blackjetrock/pak-gadget/eclipse/pak-gadget/scope_traces/rl_ram_siz1.jpg

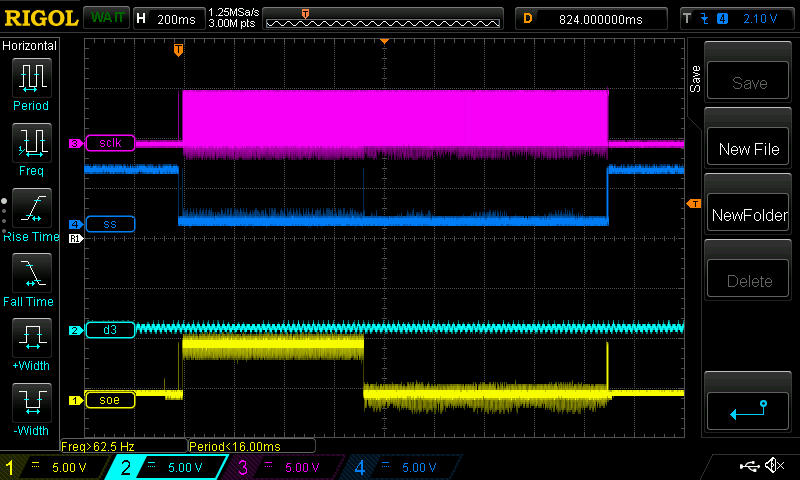
eclipse/pak-gadget/scope_traces/rl_ram_siz1.jpg
