blackjetrock/pak-gadget/eclipse/pak-gadget/scope_traces/g1.jpg

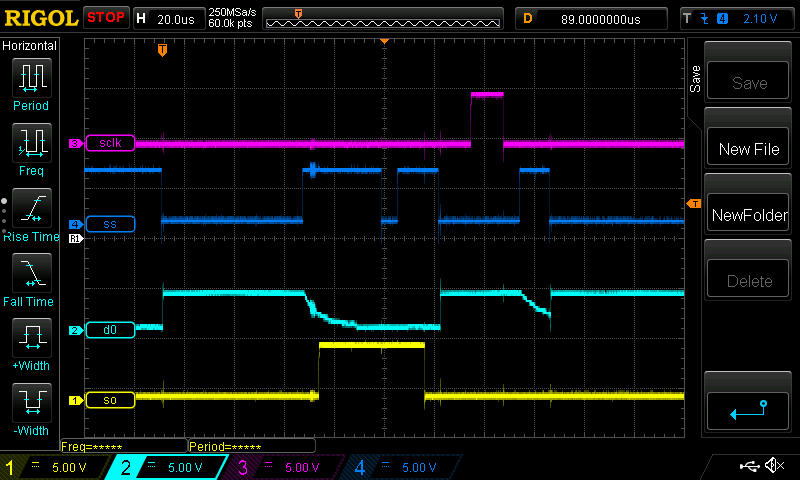
eclipse/pak-gadget/scope_traces/g1.jpg
