blackjetrock/pak-gadget/eclipse/pak-gadget/scope_traces/isr1.jpg

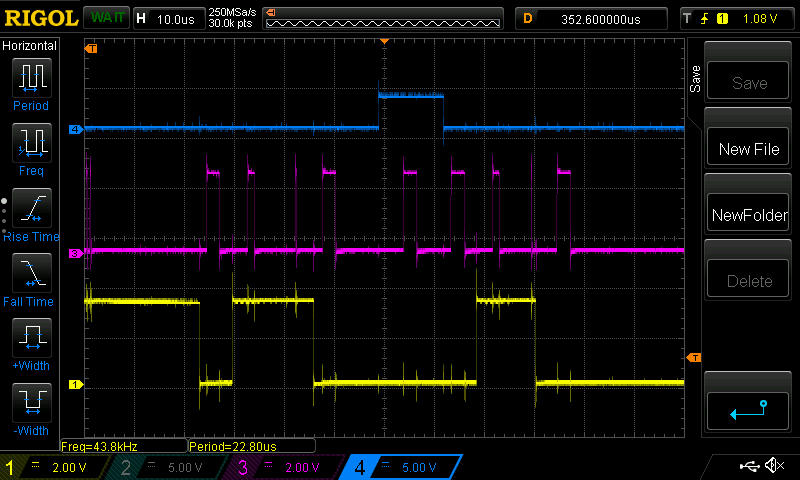
eclipse/pak-gadget/scope_traces/isr1.jpg
