blackjetrock/pak-gadget/eclipse/pak-gadget/scope_traces/NewFile1.jpg

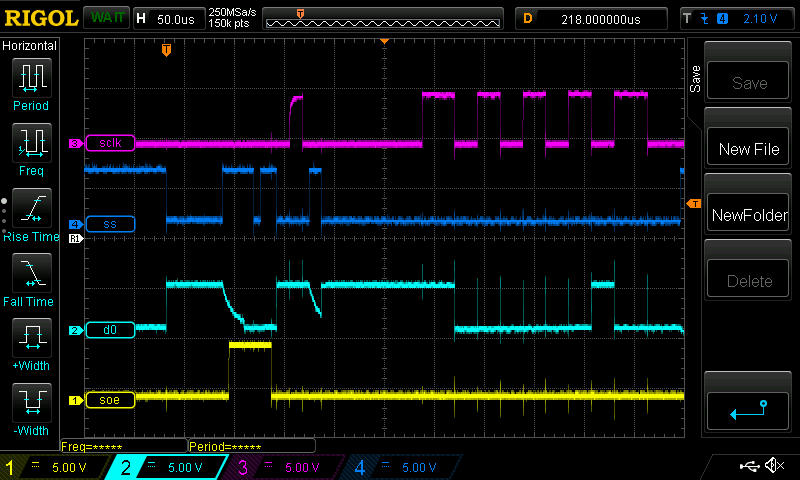
eclipse/pak-gadget/scope_traces/NewFile1.jpg
