blackjetrock/pak-gadget/eclipse/pak-gadget/scope_traces/NewFile4.jpg

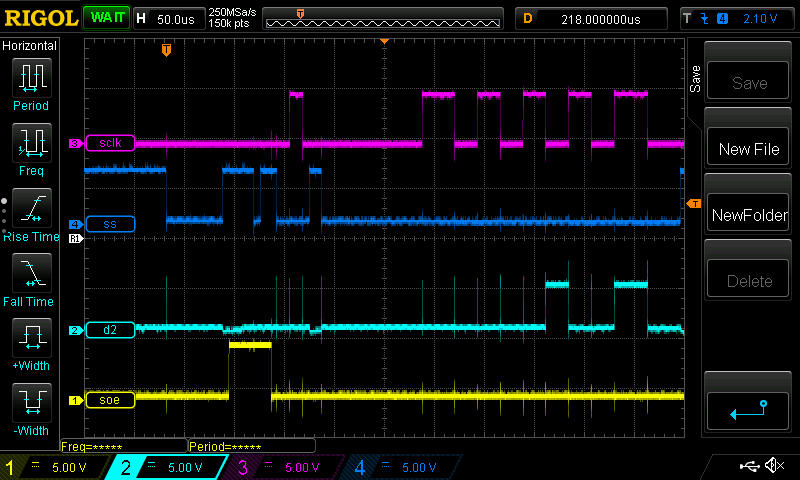
eclipse/pak-gadget/scope_traces/NewFile4.jpg
