blackjetrock/pak-gadget/eclipse/pak-gadget/scope_traces/NewFile7.jpg

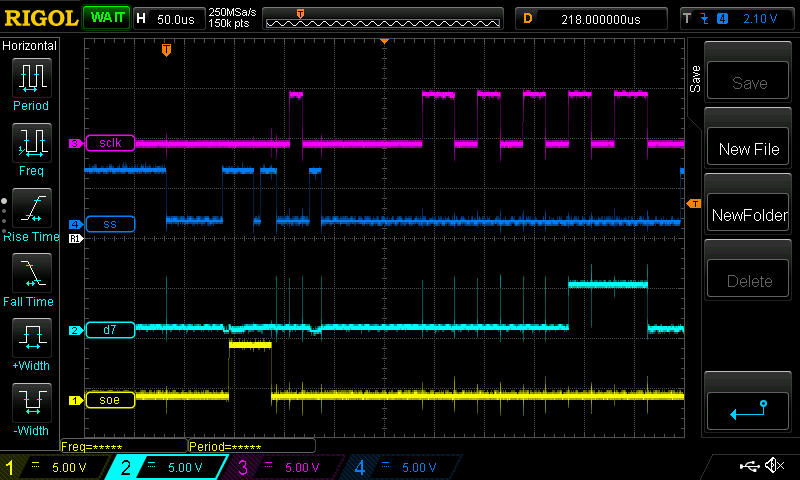
eclipse/pak-gadget/scope_traces/NewFile7.jpg
