blackjetrock/pak-gadget/eclipse/pak-gadget/scope_traces/NewFile9.jpg

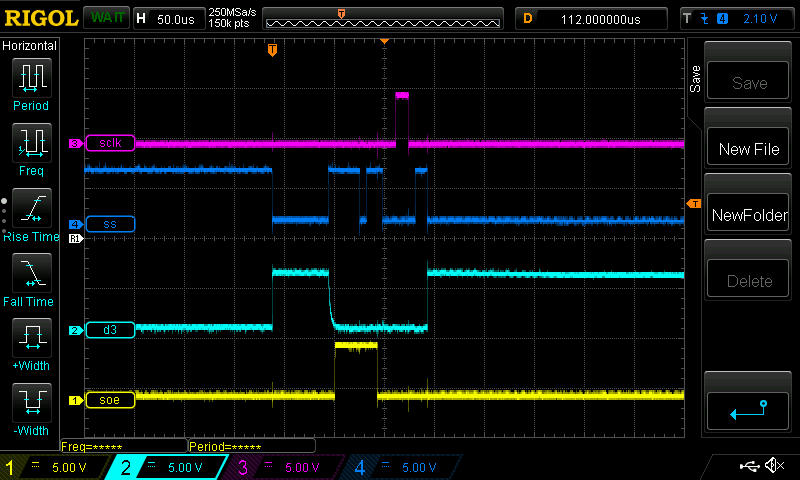
eclipse/pak-gadget/scope_traces/NewFile9.jpg
