blackjetrock/pak-gadget/eclipse/pak-gadget/scope_traces/NewFile10.jpg

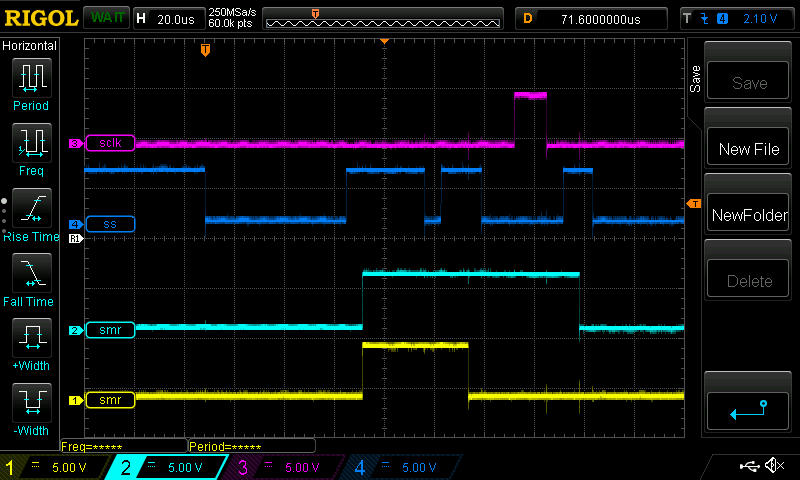
eclipse/pak-gadget/scope_traces/NewFile10.jpg
