blackjetrock/pak-gadget/eclipse/pak-gadget/scope_traces/on1.jpg

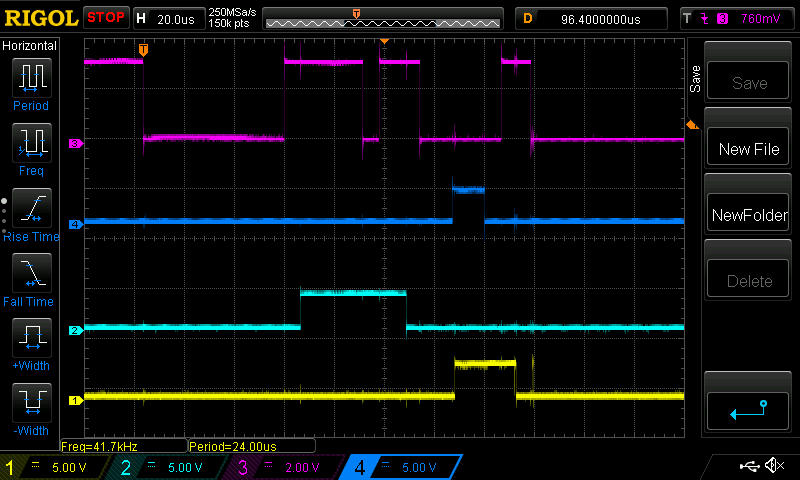
eclipse/pak-gadget/scope_traces/on1.jpg
