blackjetrock/pak-gadget/eclipse/pak-gadget/scope_traces/on1b.jpg

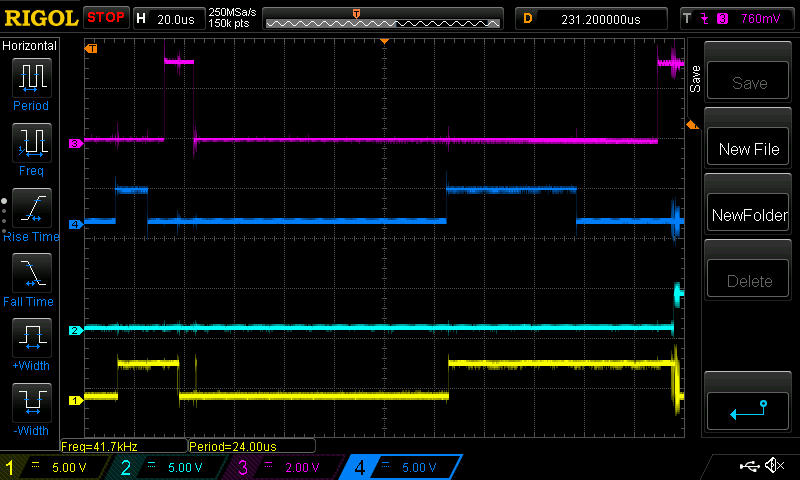
eclipse/pak-gadget/scope_traces/on1b.jpg
