blackjetrock/pak-gadget/eclipse/pak-gadget/scope_traces/on2.jpg

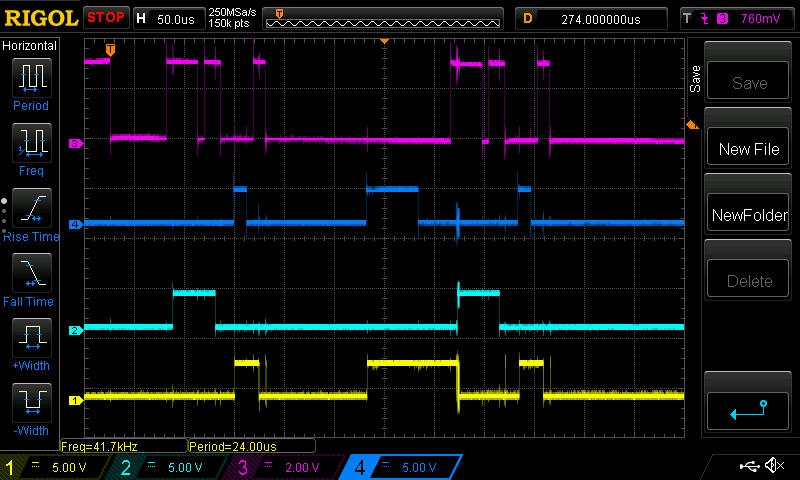
eclipse/pak-gadget/scope_traces/on2.jpg
