blackjetrock/pak-gadget/eclipse/pak-gadget/scope_traces/RAMPAK1.jpg

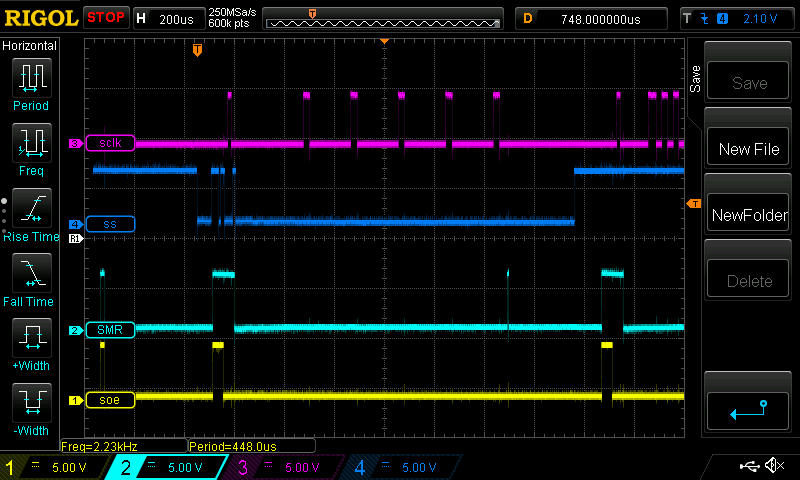
eclipse/pak-gadget/scope_traces/RAMPAK1.jpg
