blackjetrock/pak-gadget/eclipse/pak-gadget/scope_traces/RAMPAK2.jpg

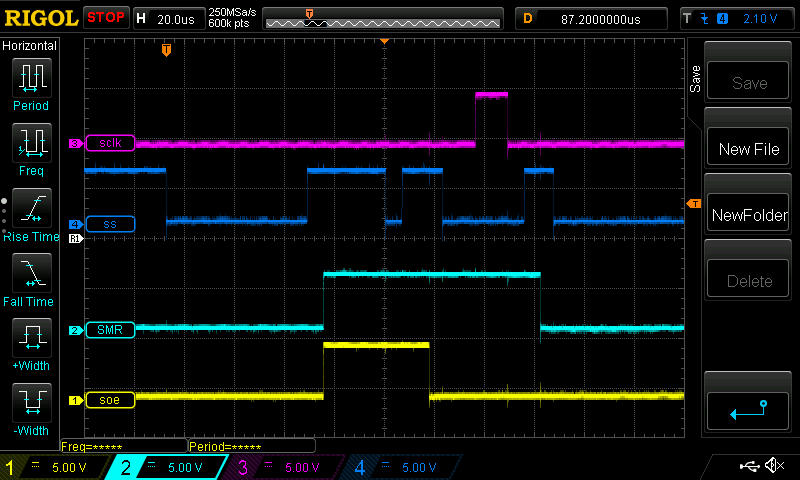
eclipse/pak-gadget/scope_traces/RAMPAK2.jpg
