blackjetrock/pak-gadget/eclipse/pak-gadget/scope_traces/RAMPAK3.jpg

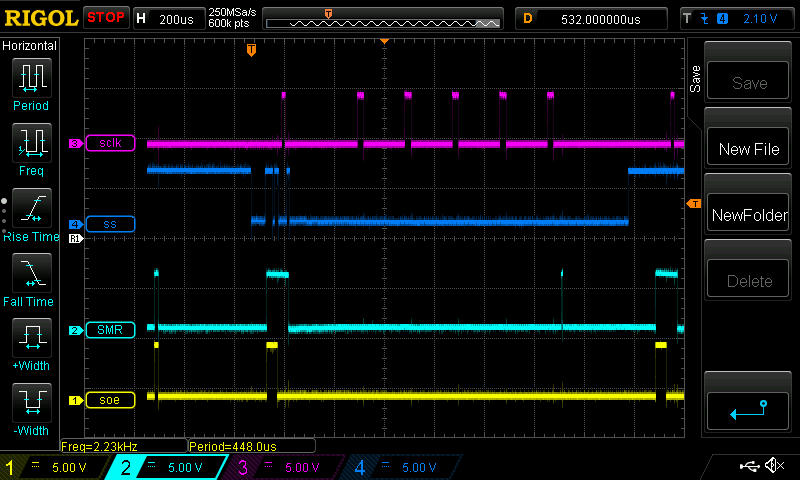
eclipse/pak-gadget/scope_traces/RAMPAK3.jpg
