blackjetrock/pak-gadget/eclipse/pak-gadget/scope_traces/RDONLY1.jpg

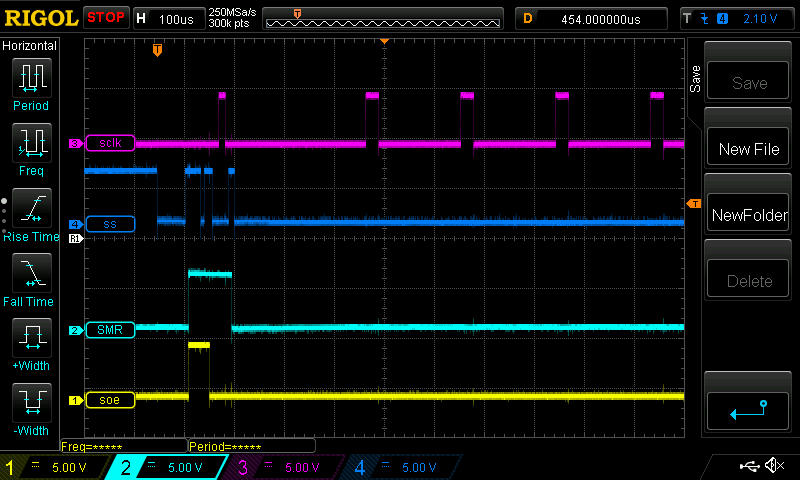
eclipse/pak-gadget/scope_traces/RDONLY1.jpg
