blackjetrock/pak-gadget/eclipse/pak-gadget/scope_traces/rl_ep1.jpg

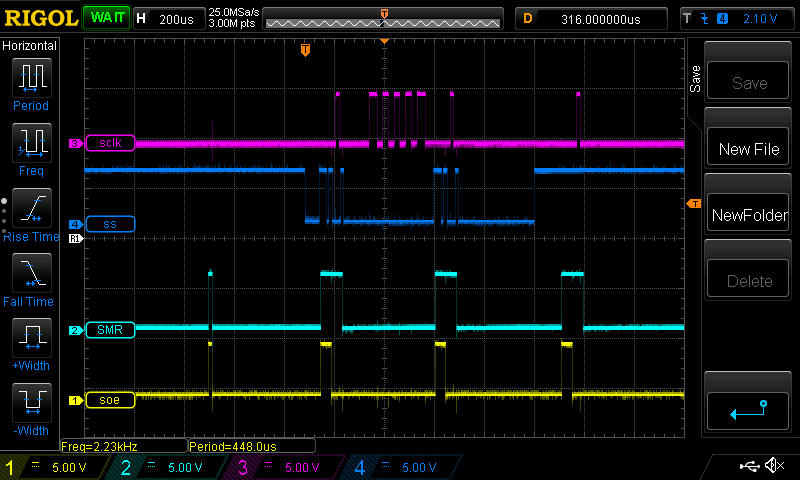
eclipse/pak-gadget/scope_traces/rl_ep1.jpg
