blackjetrock/pak-gadget/eclipse/pak-gadget/scope_traces/rl_ep2.jpg

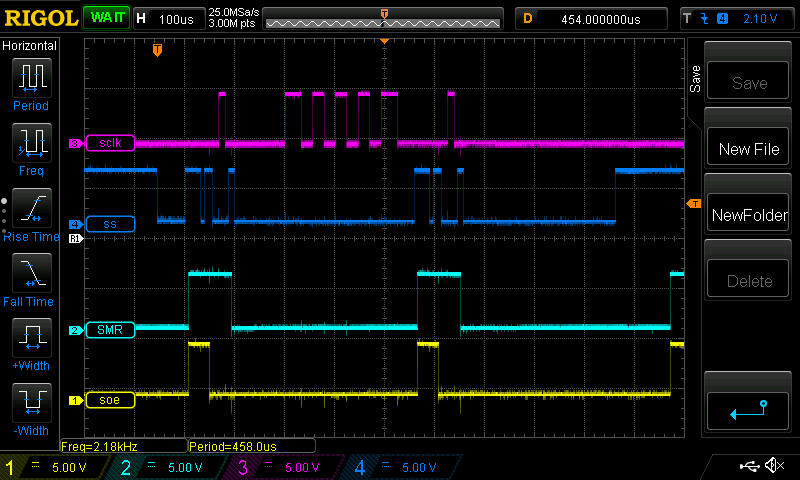
eclipse/pak-gadget/scope_traces/rl_ep2.jpg
