blackjetrock/pak-gadget/eclipse/pak-gadget/scope_traces/rl_ep3.jpg

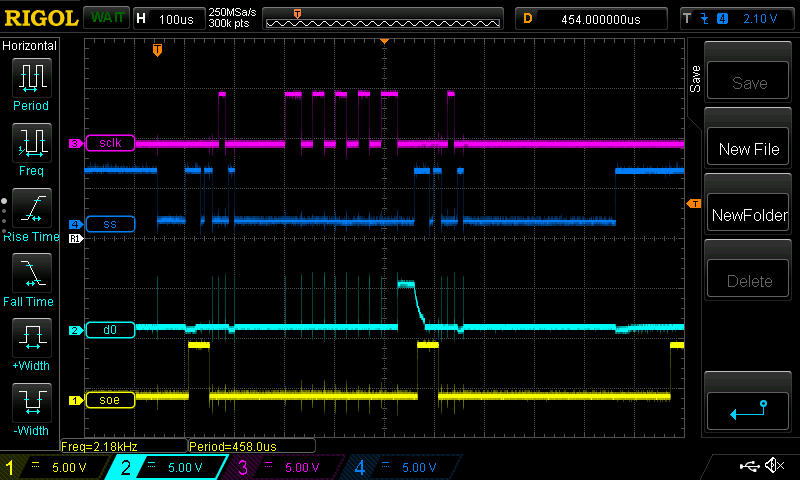
eclipse/pak-gadget/scope_traces/rl_ep3.jpg
