blackjetrock/pak-gadget/eclipse/pak-gadget/scope_traces/rl_ep_pgm.jpg

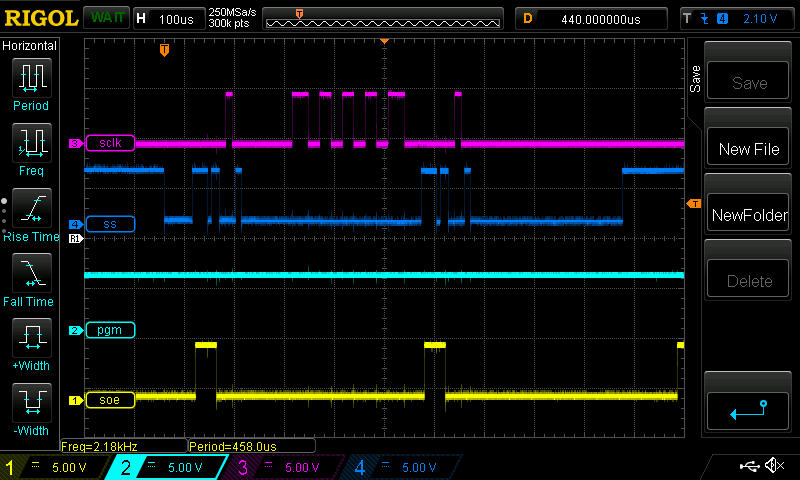
eclipse/pak-gadget/scope_traces/rl_ep_pgm.jpg
