blackjetrock/pak-gadget/eclipse/pak-gadget/scope_traces/rl_epd1.jpg

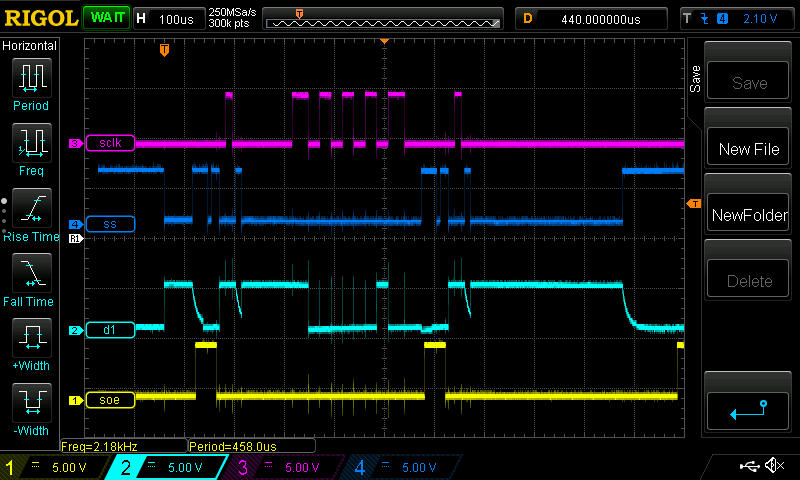
eclipse/pak-gadget/scope_traces/rl_epd1.jpg
