blackjetrock/pak-gadget/eclipse/pak-gadget/scope_traces/rl_ra1.jpg

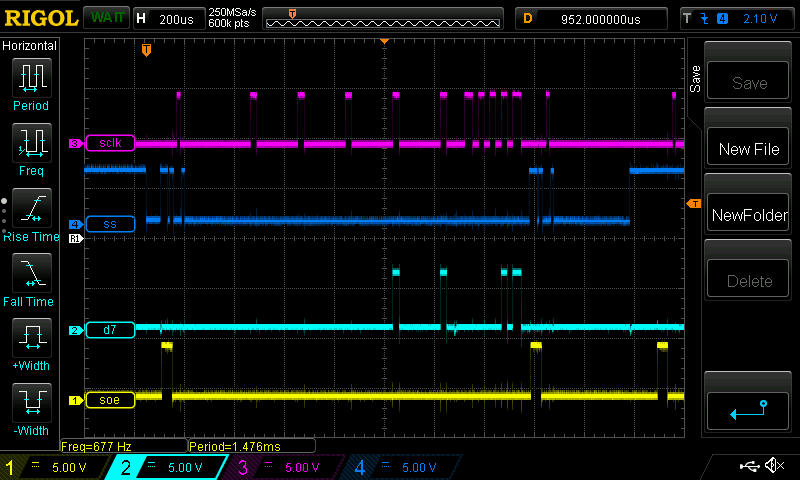
eclipse/pak-gadget/scope_traces/rl_ra1.jpg
