blackjetrock/pak-gadget/eclipse/pak-gadget/scope_traces/rra1.jpg

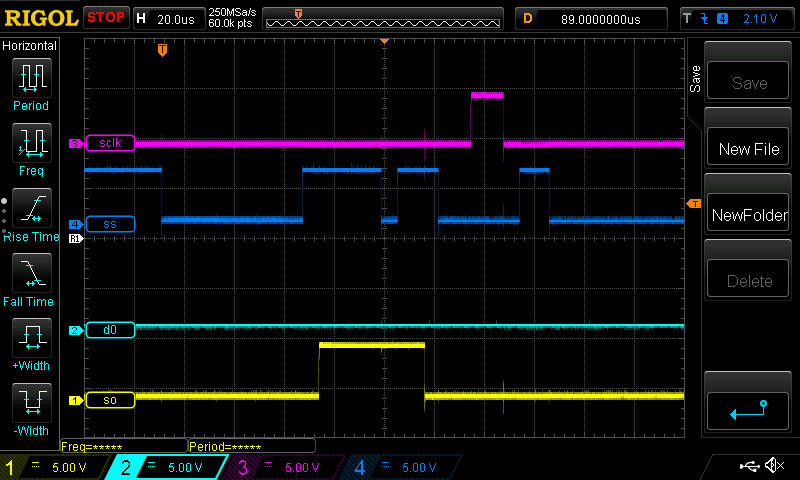
eclipse/pak-gadget/scope_traces/rra1.jpg
