blackjetrock/pak-gadget/eclipse/pak-gadget/scope_traces/rra3.jpg

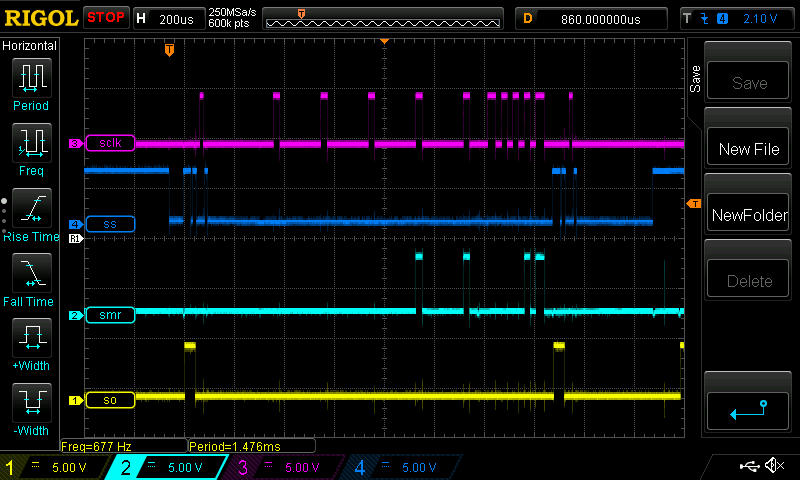
eclipse/pak-gadget/scope_traces/rra3.jpg
