blackjetrock/pak-gadget/pack_breakout/pak_breakout.sch

## KiCad design pack_breakout/pak_breakout.sch (2021-11-20)

Schematic: pak_breakout.sch

Parts:
C1: 1uF; C_0805_2012Metric
C2, C5: 100nF; C_0805_2012Metric
D1: D_Schottky; D_SOD-123
J1: Conn_02x08_Odd_Even; Psion_datapak_2x08_P2.54mm_Horizontal
J2: Conn_01x06_Female; PinSocket_1x06_P2.54mm_Vertical
J3: Conn_01x04_Female; PinHeader_1x04_P2.54mm_Vertical
J4: Conn_01x02_Female; PinHeader_1x02_P2.54mm_Vertical
J5: Conn_01x03_Female; PinHeader_1x03_P2.54mm_Vertical
JP1, JP2, JP3, JP4: Jumper_NO_Small; SolderJumper-2_P1.3mm_Open_RoundedPad1.0x1.5mm
R1, R2, R3, R20: 47k; R_0805_2012Metric
R5, R7: 4k7; R_0805_2012Metric
R6, R8, R9, R19: R_Small; R_0805_2012Metric
SW1, SW2, SW3, SW4: sw; SW_PUSH-12mm
U1, U2: 74LS245; SOIC-20W_7.5x12.8mm_P1.27mm
U3: Pico; RPi_Pico_SMD_TH
XS1: SD_ebay-uSD-push_push_SMD; Conn_uSDcard
